RoboticsBrno/RB0004-NeopixelBooster/evaluation/assets/guide/19.jpg

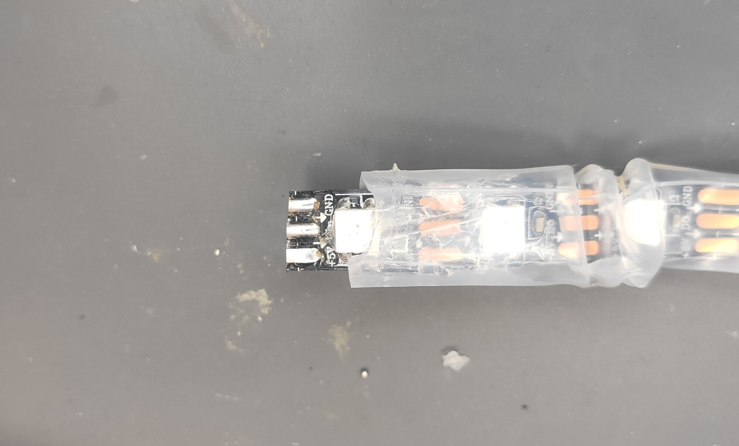
evaluation/assets/guide/19.jpg
