RoboticsBrno/RB0004-NeopixelBooster/evaluation/assets/guide/34.jpg

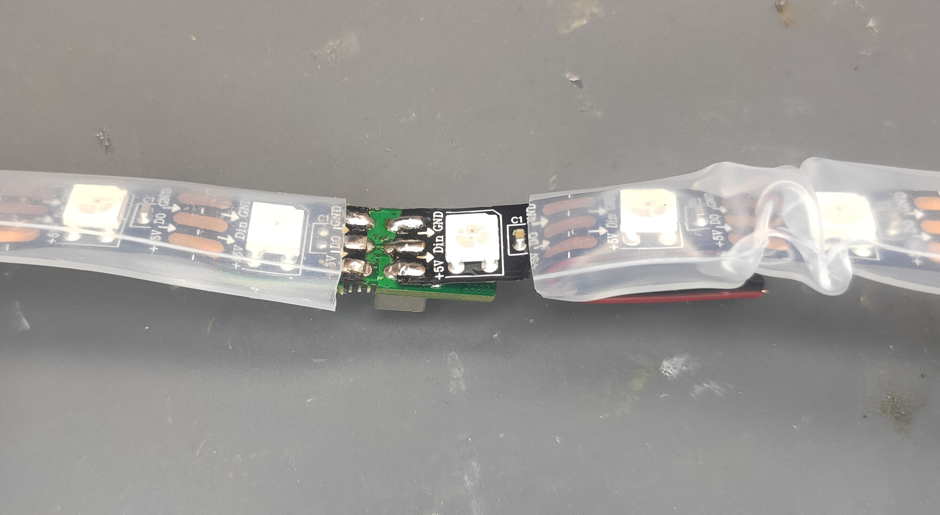
evaluation/assets/guide/34.jpg
