RoboticsBrno/RB0004-NeopixelBooster/evaluation/assets/back.png

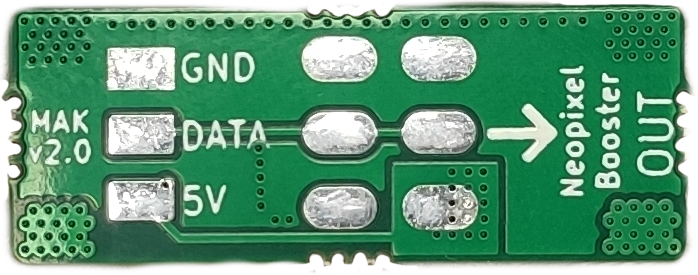
evaluation/assets/back.png
