RoboticsBrno/RB0004-NeopixelBooster/evaluation/assets/fron.png

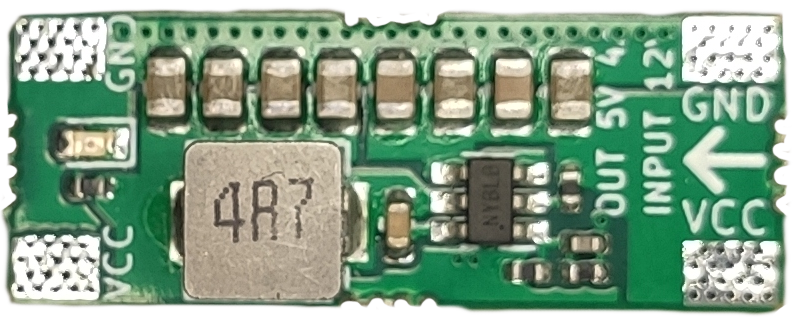
evaluation/assets/fron.png
