RoboticsBrno/RB0004-NeopixelBooster/evaluation/assets/strip.png

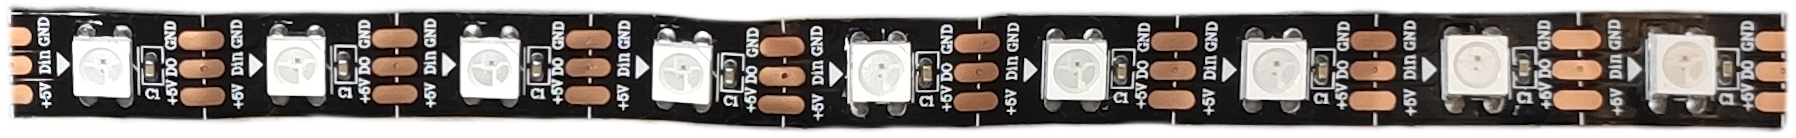
evaluation/assets/strip.png
