RoboticsBrno/RB0004-NeopixelBooster/evaluation/assets/strp-short.png

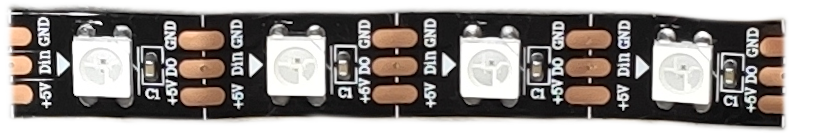
evaluation/assets/strp-short.png
