RoboticsBrno/RB0004-NeopixelBooster/evaluation/assets/waveforms/v2_1.png

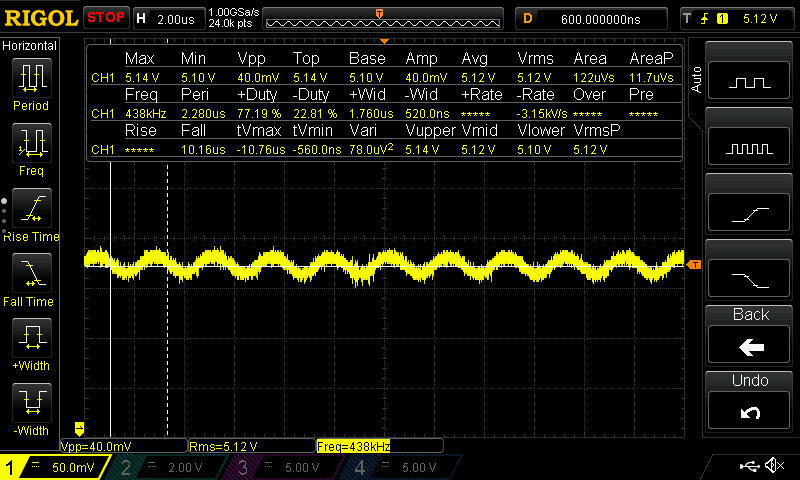
evaluation/assets/waveforms/v2_1.png
