RoboticsBrno/RB0004-NeopixelBooster/evaluation/assets/waveforms/v2_3.png

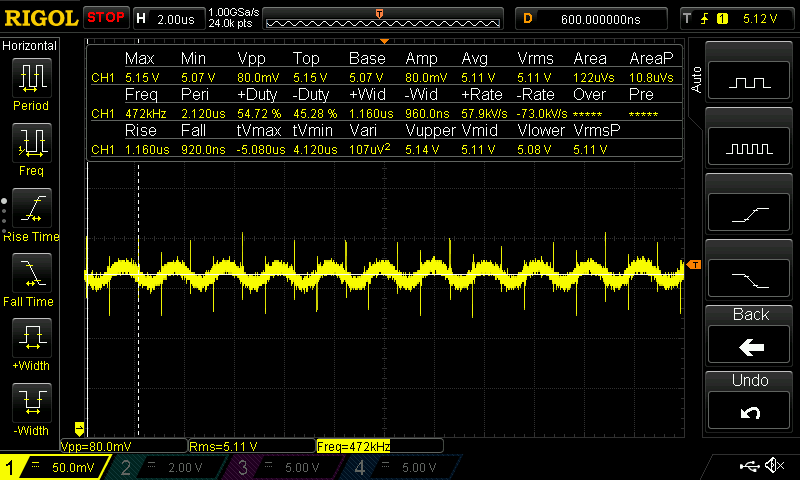
evaluation/assets/waveforms/v2_3.png
