RoboticsBrno/RB0004-NeopixelBooster/evaluation/assets/waveforms/v2_4.png

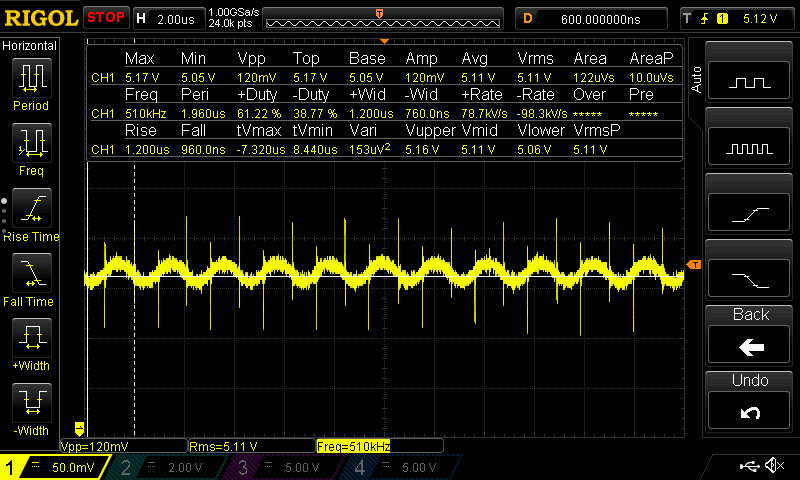
evaluation/assets/waveforms/v2_4.png
