RoboticsBrno/RB0004-NeopixelBooster/evaluation/assets/waveforms/v2_6.png

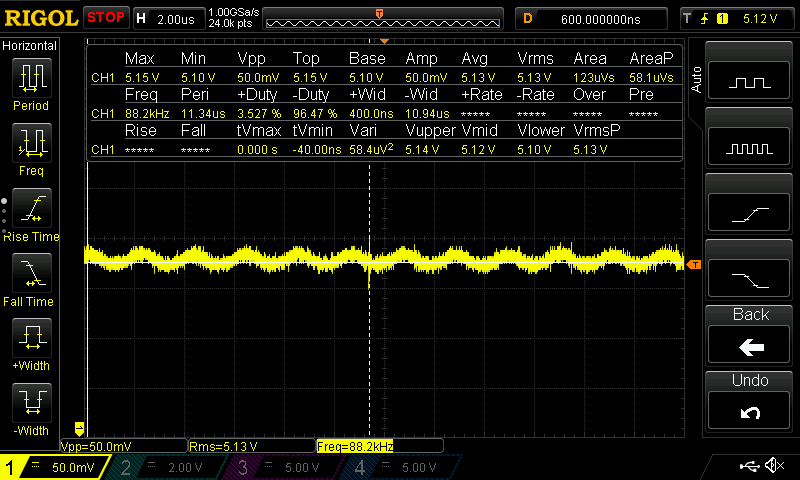
evaluation/assets/waveforms/v2_6.png
