RoboticsBrno/RB0004-NeopixelBooster/evaluation/assets/waveforms/v2_7.png

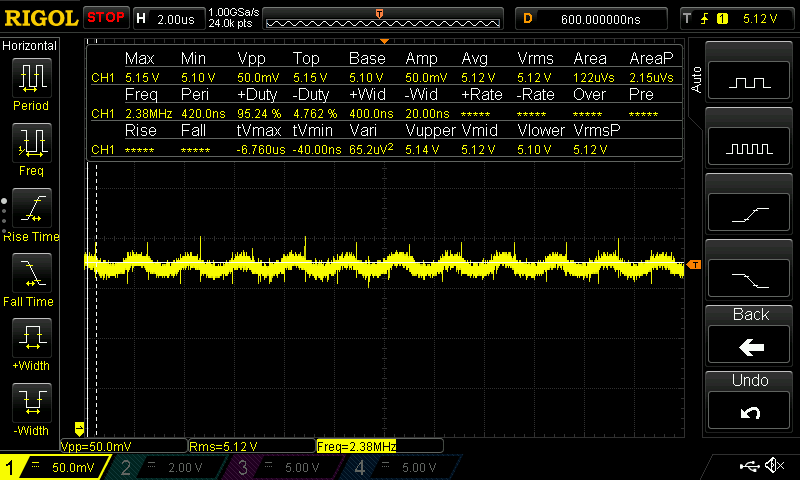
evaluation/assets/waveforms/v2_7.png
