RoboticsBrno/RB0004-NeopixelBooster/evaluation/assets/waveforms/v2_9.png

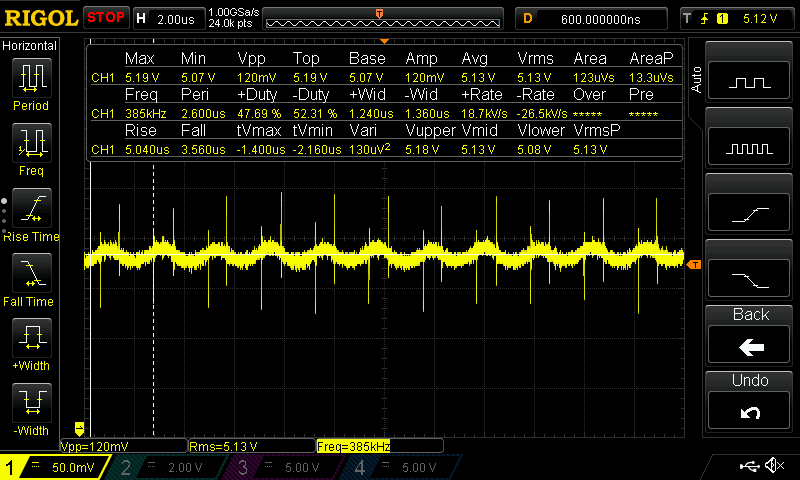
evaluation/assets/waveforms/v2_9.png
