RoboticsBrno/RB0004-NeopixelBooster/evaluation/assets/waveforms/v2_10.png

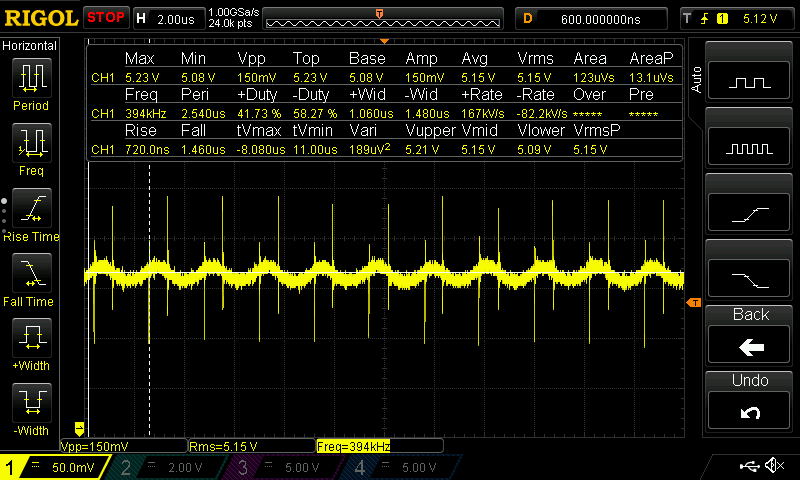
evaluation/assets/waveforms/v2_10.png
