RoboticsBrno/RB0004-NeopixelBooster/evaluation/assets/waveforms/v2_11.png

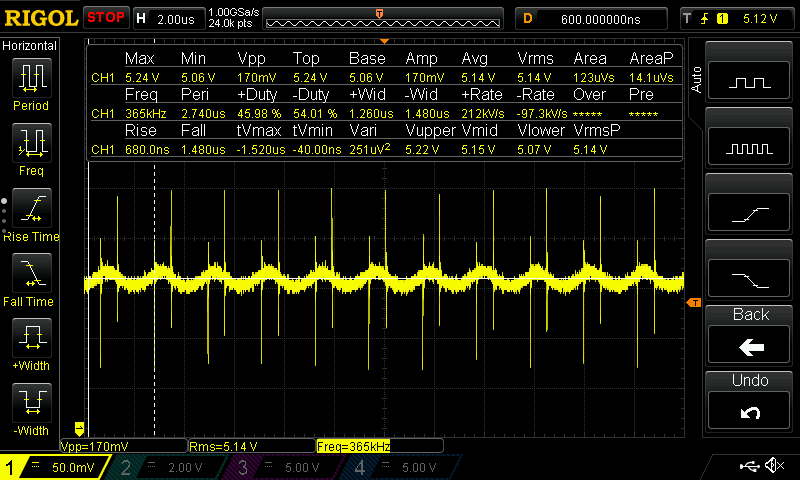
evaluation/assets/waveforms/v2_11.png
